Matei911/UpdateMate/software/updatemate_version_1/update_mate/drawNews.h

#ifndef DRAWNEWS_H
#define DRAWNEWS_H

#include "drawcmmn.h"
#include "sensorReadings.h"
#include "drawHead.h"
#include <HTTPClient.h>
#include <ArduinoJson.h>


void fullRefreshPageNews();

#endif  // DRAWPAGE3_H
